Agile-and-Adaptive-Robotics/Platform/Linsey_s Documentation/screenshots/T11_L4-Center-042418.PNG

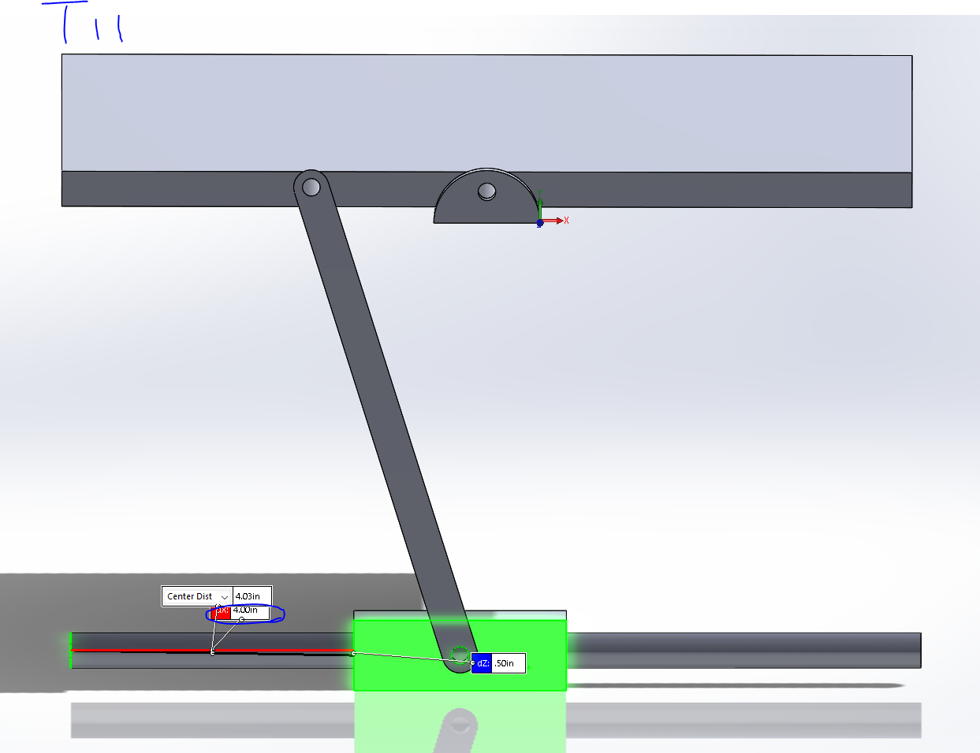
Linsey_s Documentation/screenshots/T11_L4-Center-042418.PNG
