Agile-and-Adaptive-Robotics/Platform/Linsey_s Documentation/screenshots/T2_angle-042218.PNG

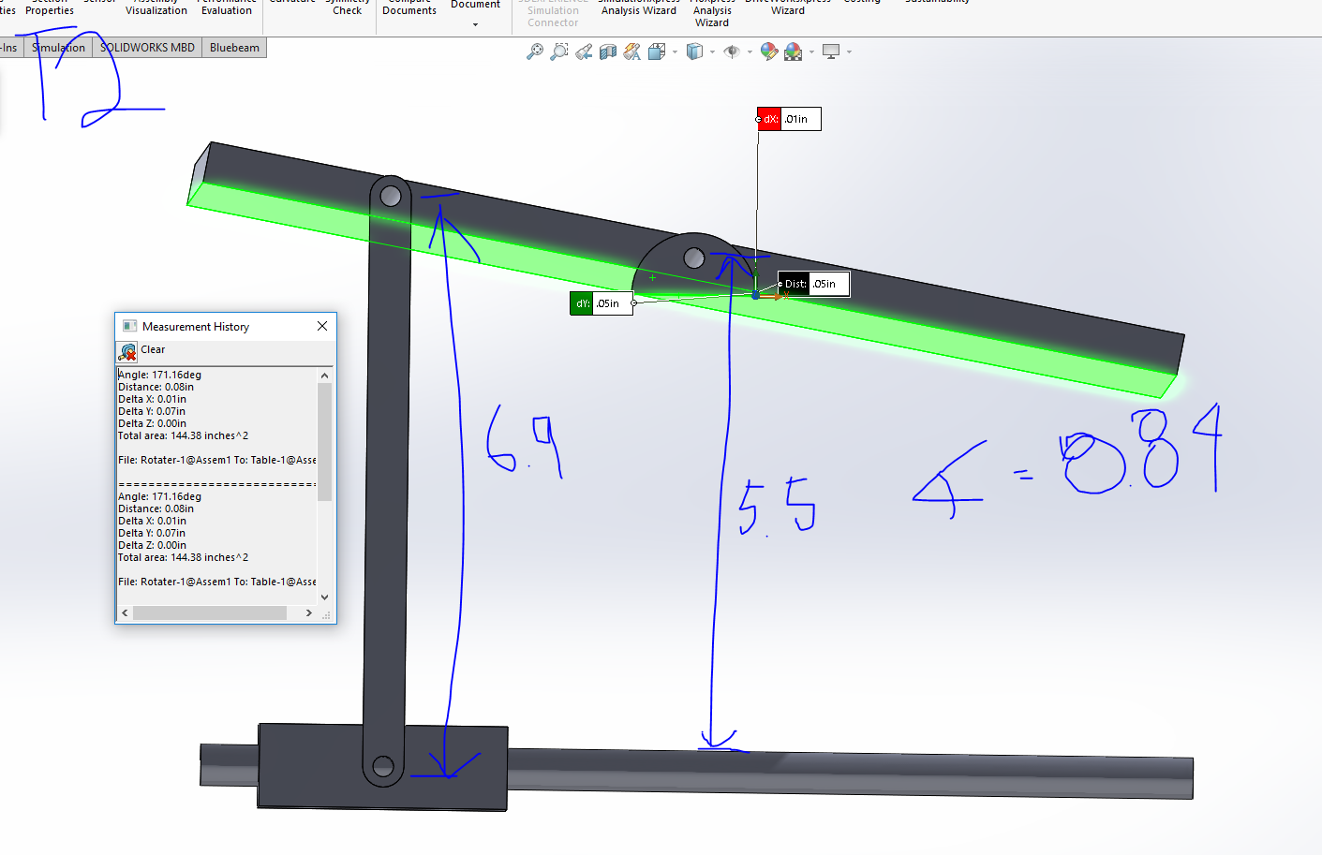
Linsey_s Documentation/screenshots/T2_angle-042218.PNG
