Agile-and-Adaptive-Robotics/Platform/Linsey_s Documentation/screenshots/T4_angle-042218.PNG

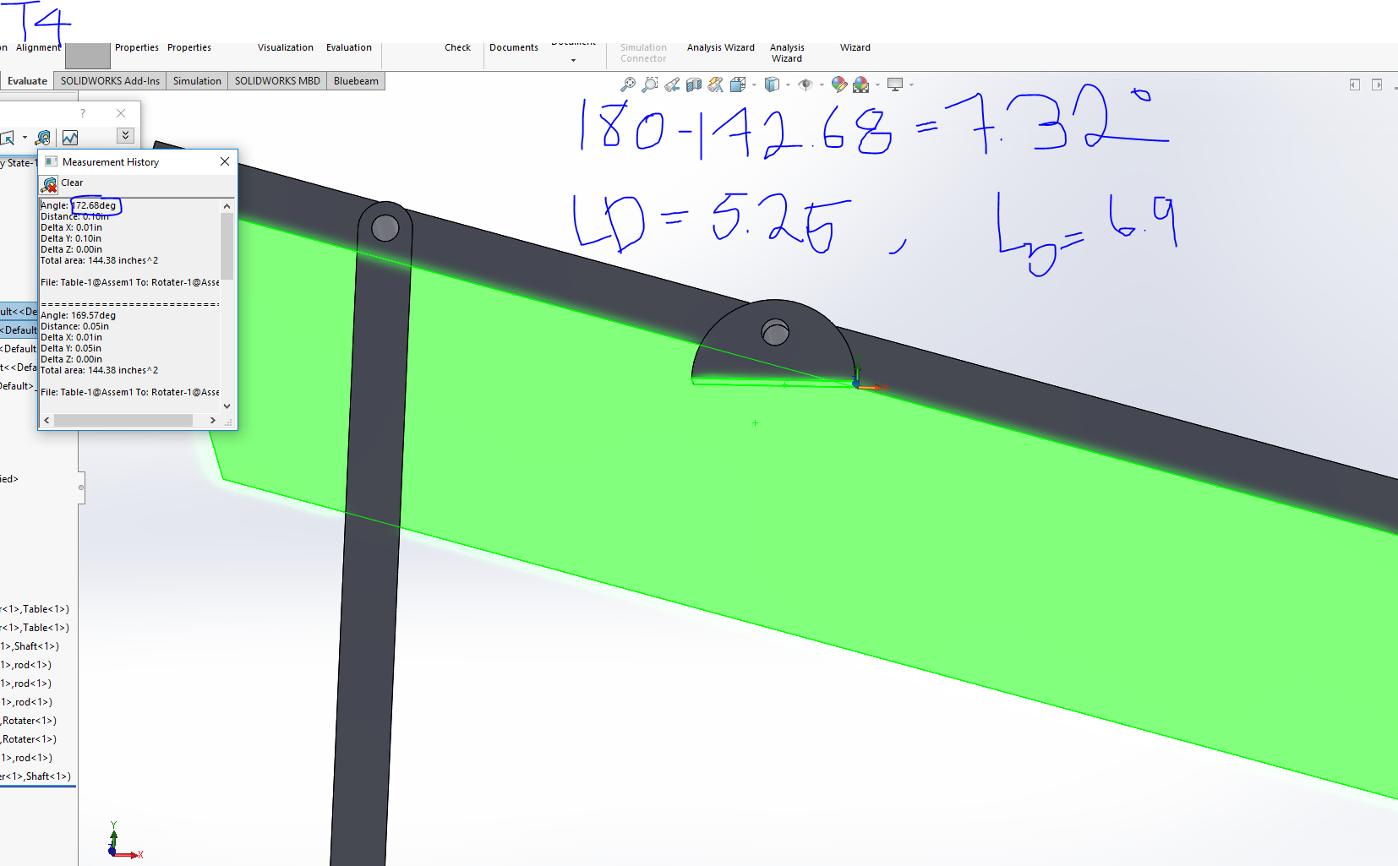
Linsey_s Documentation/screenshots/T4_angle-042218.PNG
