Agile-and-Adaptive-Robotics/Platform/Linsey_s Documentation/screenshots/T5_angle-042318.PNG

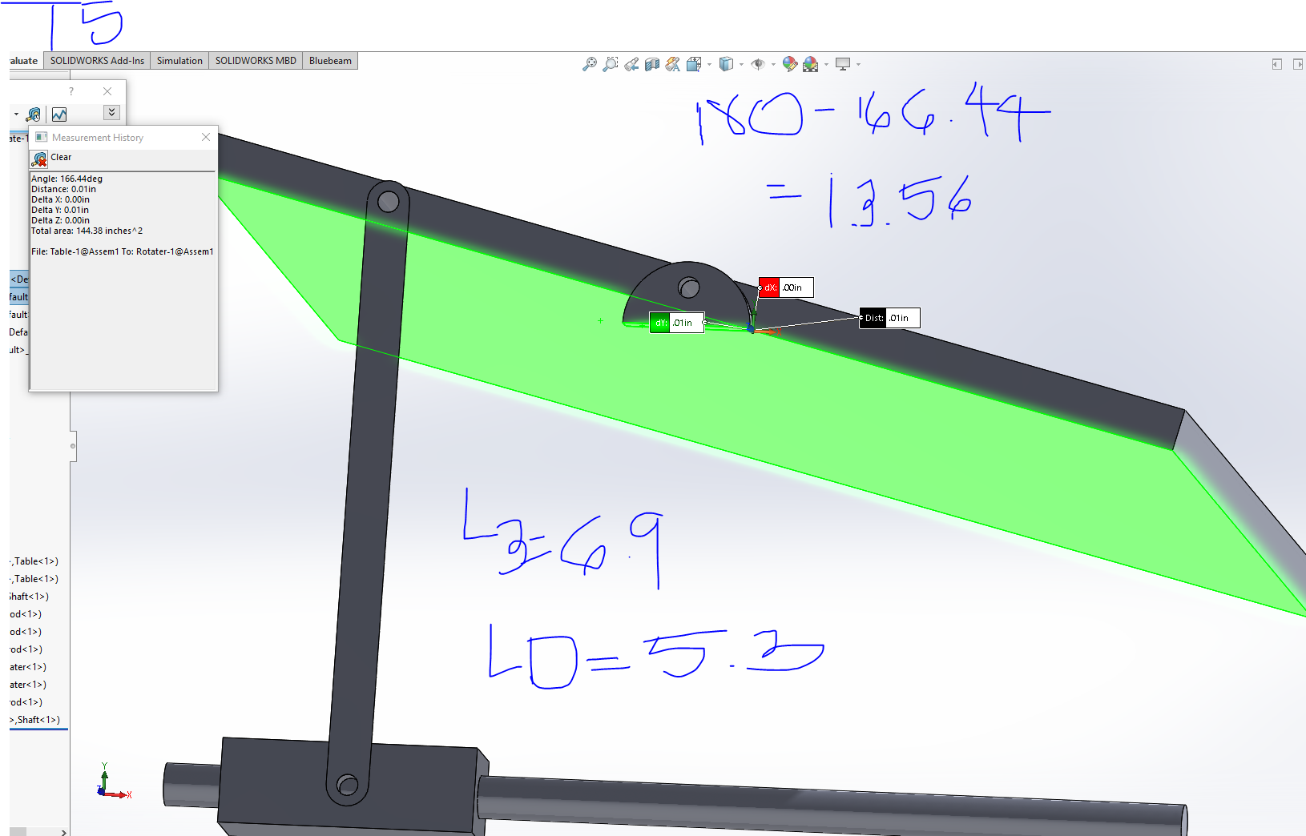
Linsey_s Documentation/screenshots/T5_angle-042318.PNG
