Agile-and-Adaptive-Robotics/Platform/Linsey_s Documentation/screenshots/T7_angle-042318.PNG

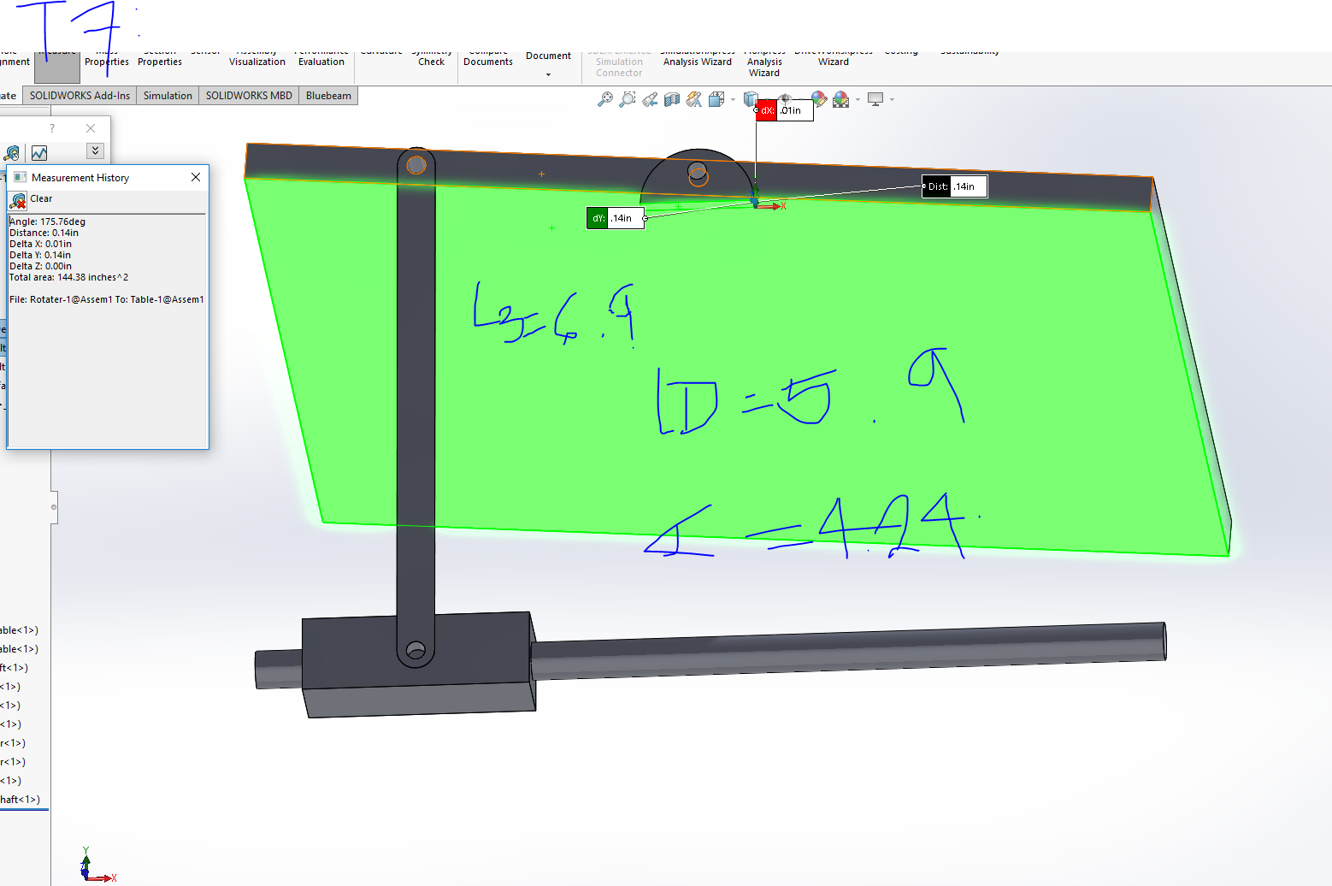
Linsey_s Documentation/screenshots/T7_angle-042318.PNG
