Agile-and-Adaptive-Robotics/Platform/Linsey_s Documentation/screenshots/T8_angle-042418-L2.PNG

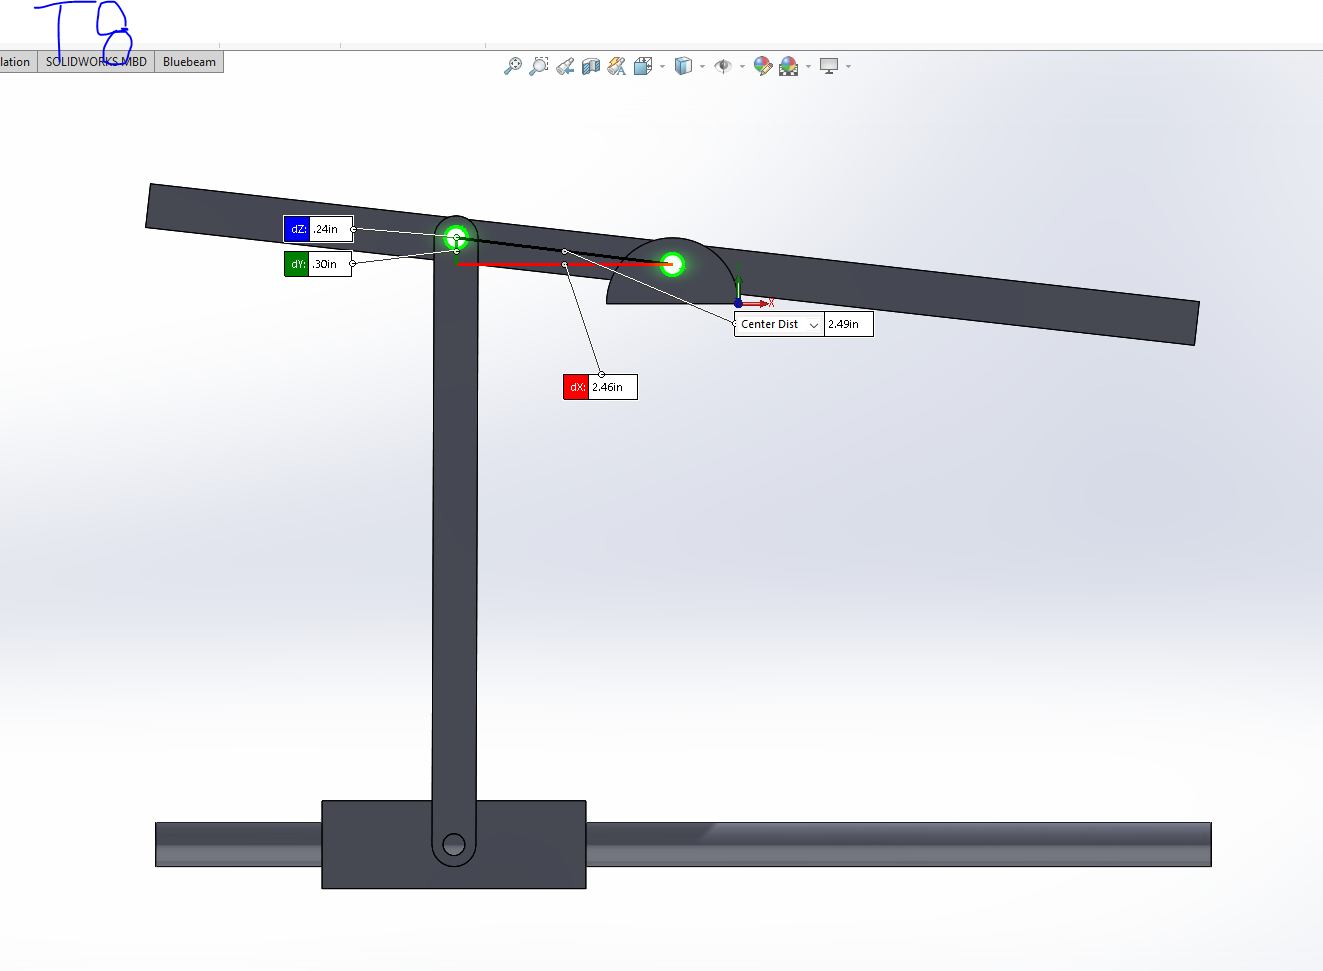
Linsey_s Documentation/screenshots/T8_angle-042418-L2.PNG
