Agile-and-Adaptive-Robotics/Platform/Linsey_s Documentation/screenshots/T9_angle-042418.PNG

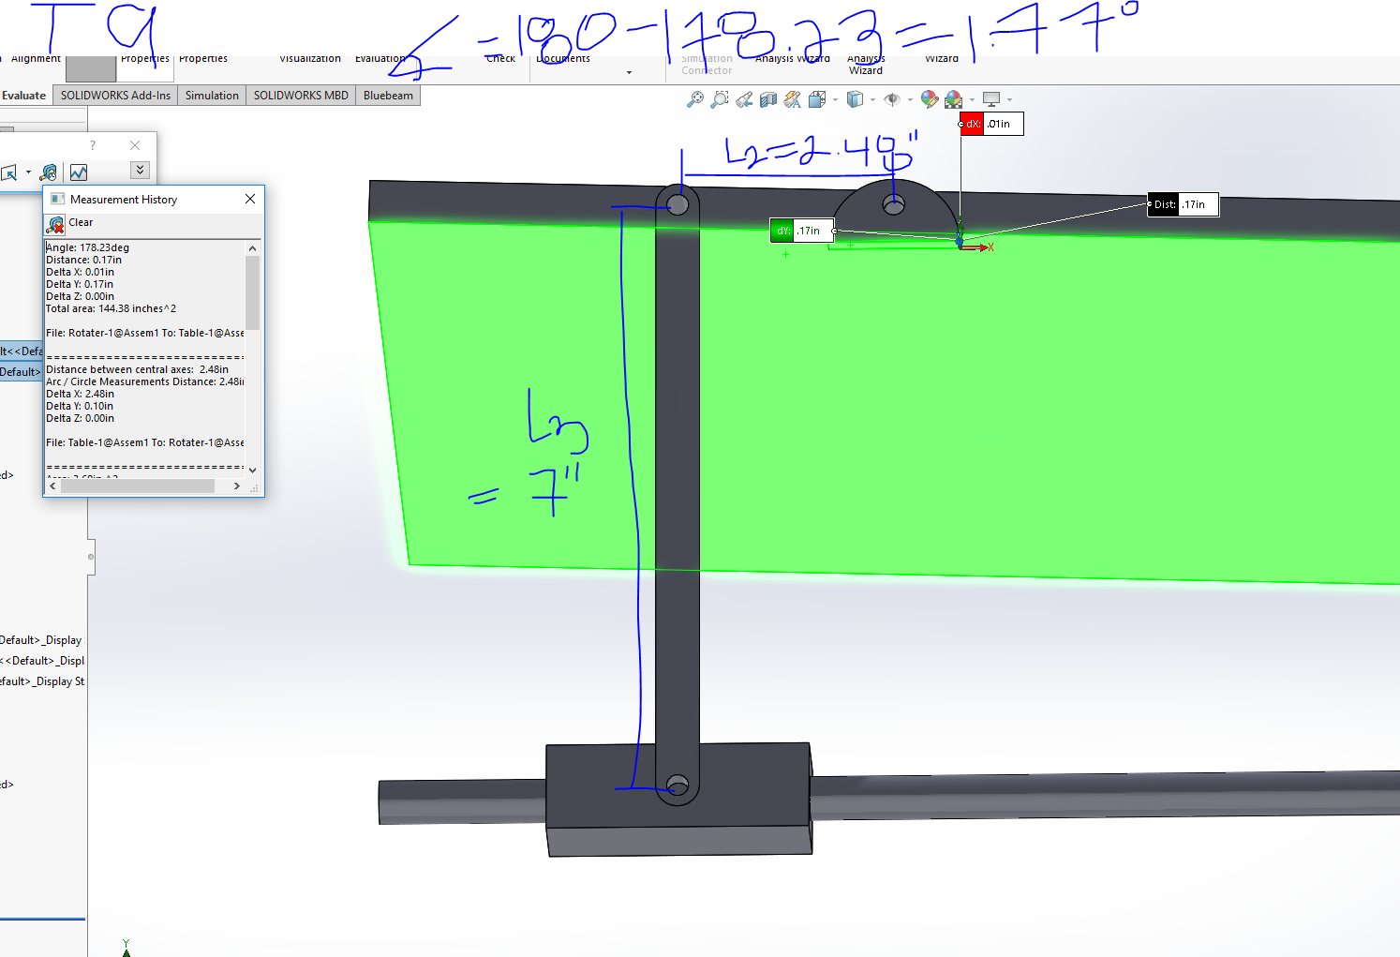
Linsey_s Documentation/screenshots/T9_angle-042418.PNG
