Agile-and-Adaptive-Robotics/Platform/Linsey_s Documentation/screenshots/T10_angle-042418.PNG

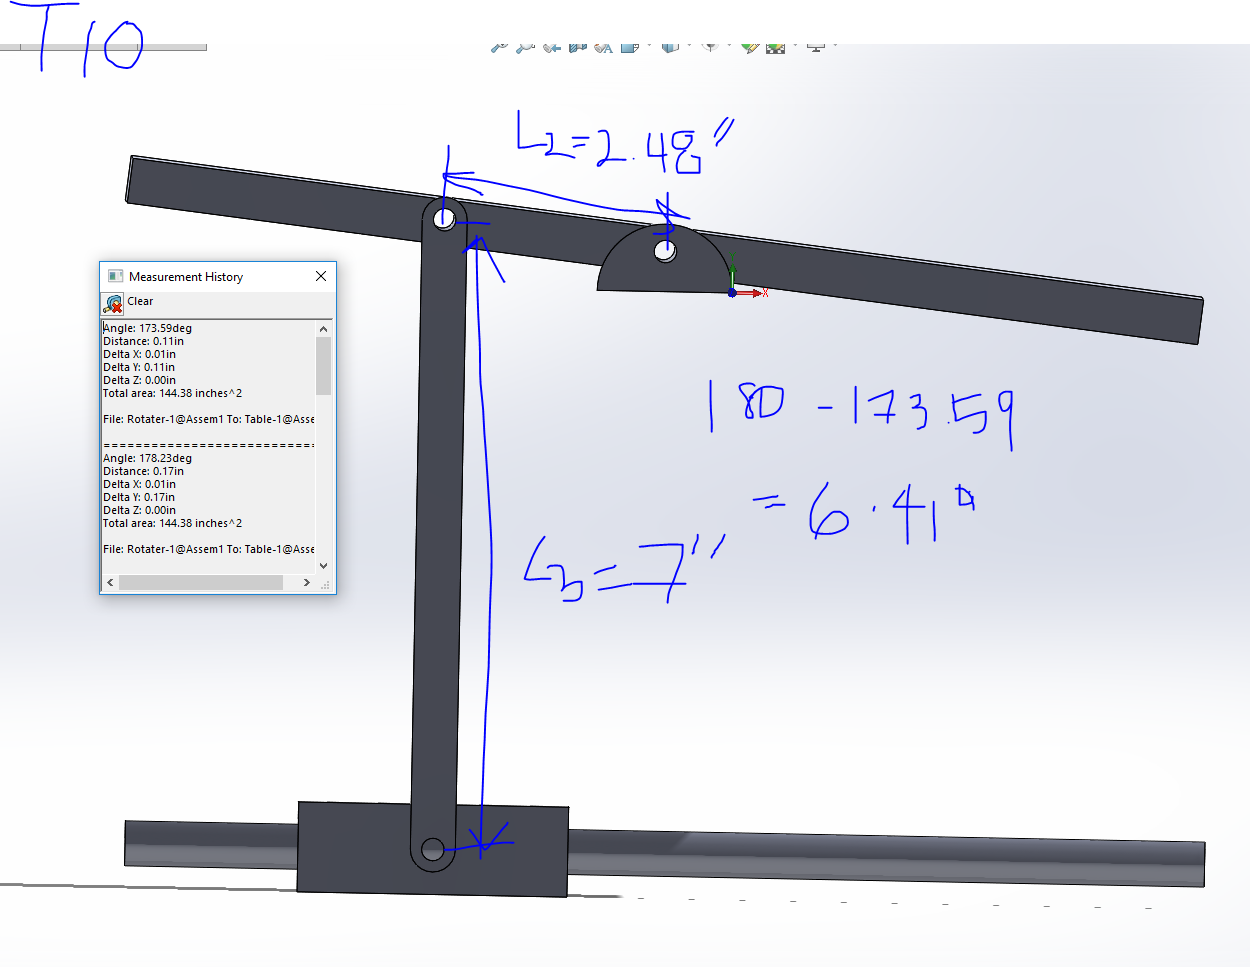
Linsey_s Documentation/screenshots/T10_angle-042418.PNG
