Agile-and-Adaptive-Robotics/Platform/Linsey_s Documentation/screenshots/T11_L4-left.PNG

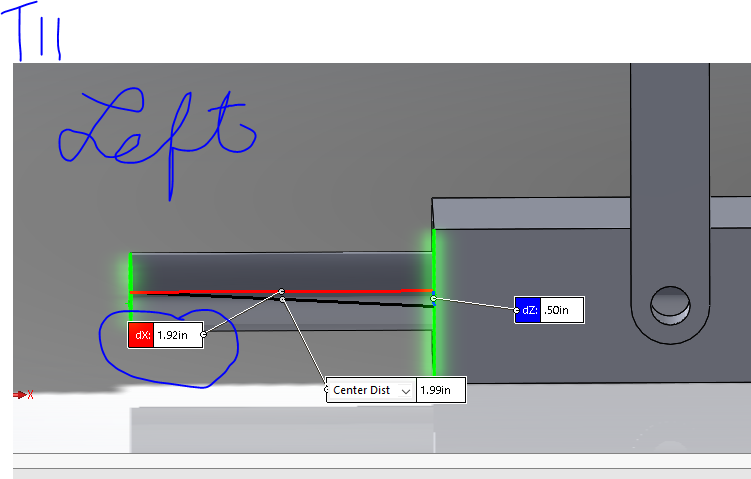
Linsey_s Documentation/screenshots/T11_L4-left.PNG
