Agile-and-Adaptive-Robotics/Platform/Linsey_s Documentation/screenshots/T11_triangles-1.PNG

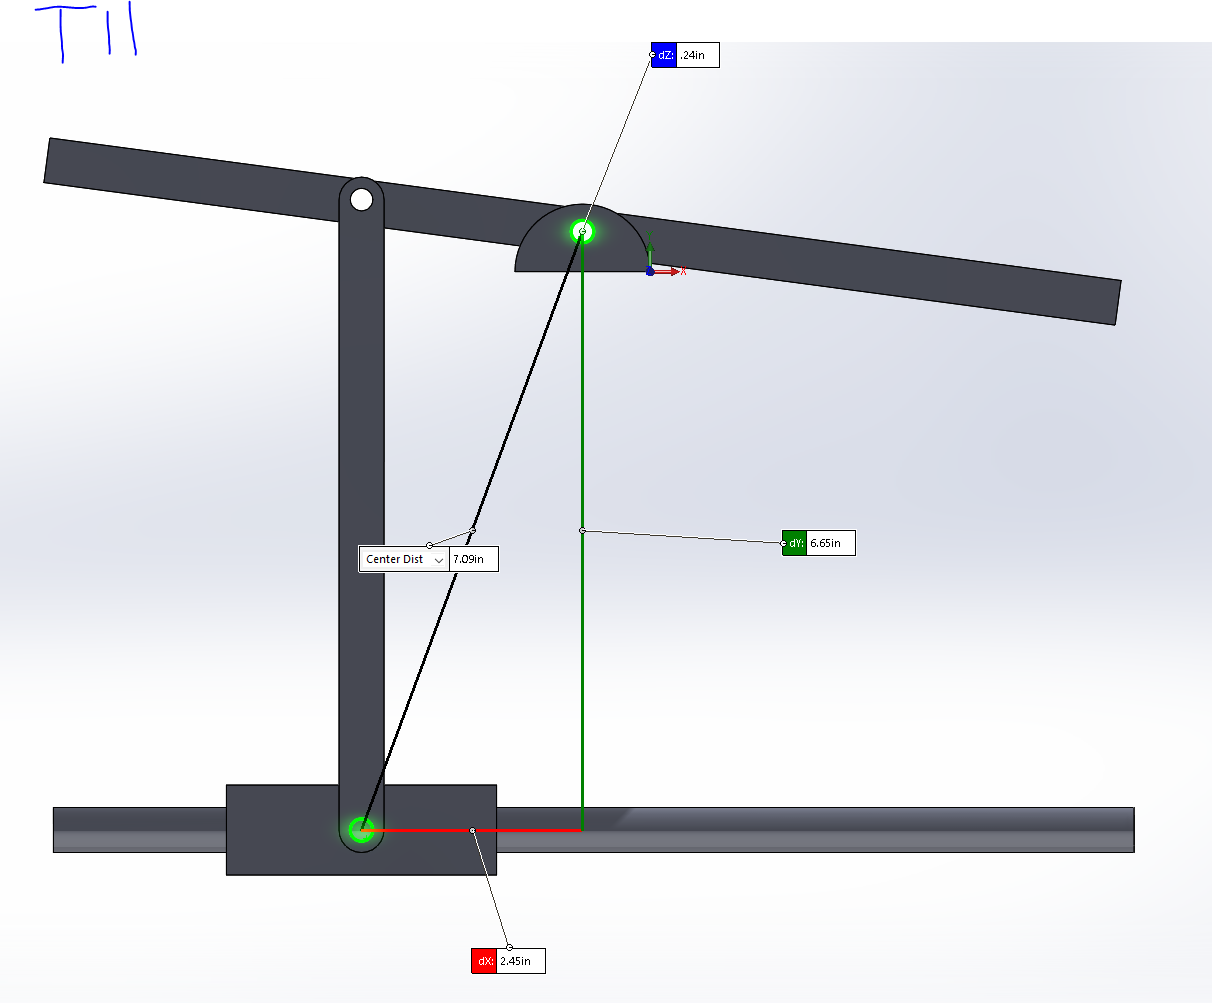
Linsey_s Documentation/screenshots/T11_triangles-1.PNG
