Agile-and-Adaptive-Robotics/Platform/Linsey_s Documentation/screenshots/Works_1-FindL4pt1.PNG

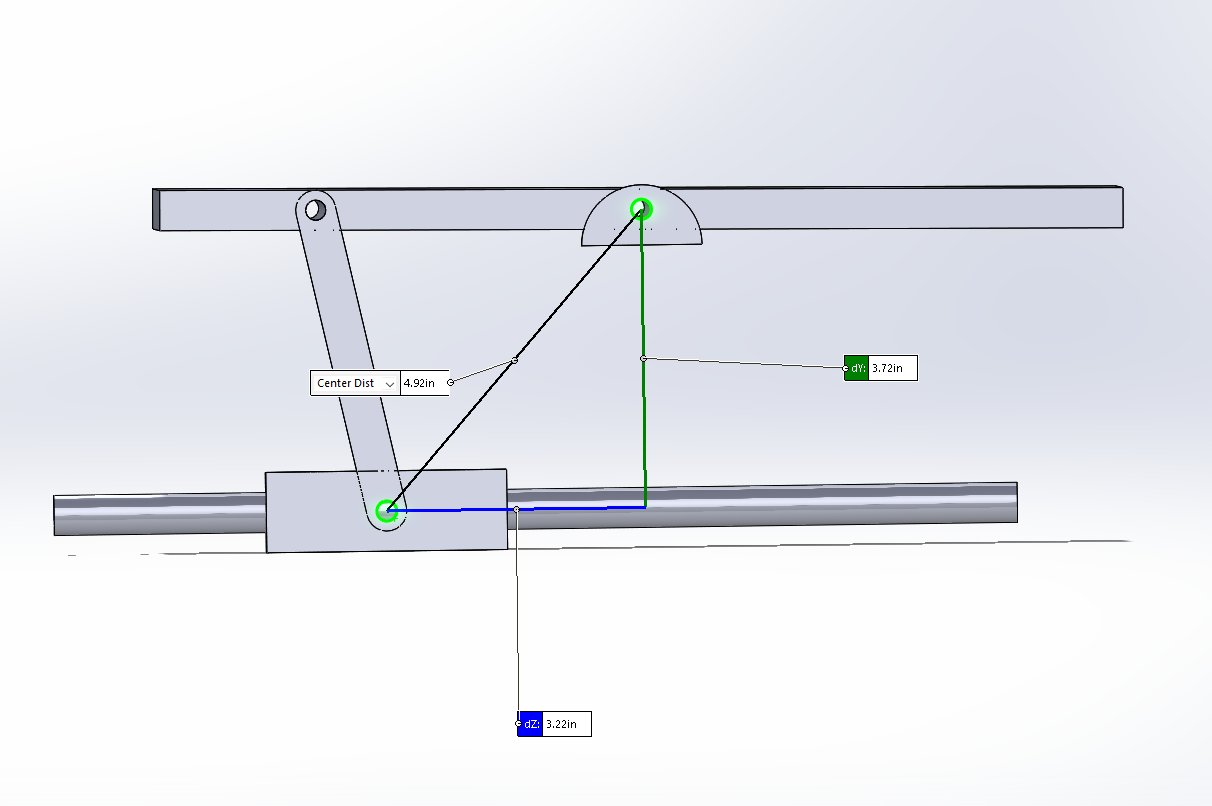
Linsey_s Documentation/screenshots/Works_1-FindL4pt1.PNG
