Agile-and-Adaptive-Robotics/Platform/Linsey_s Documentation/screenshots/Works_1-FindL4pt2.PNG

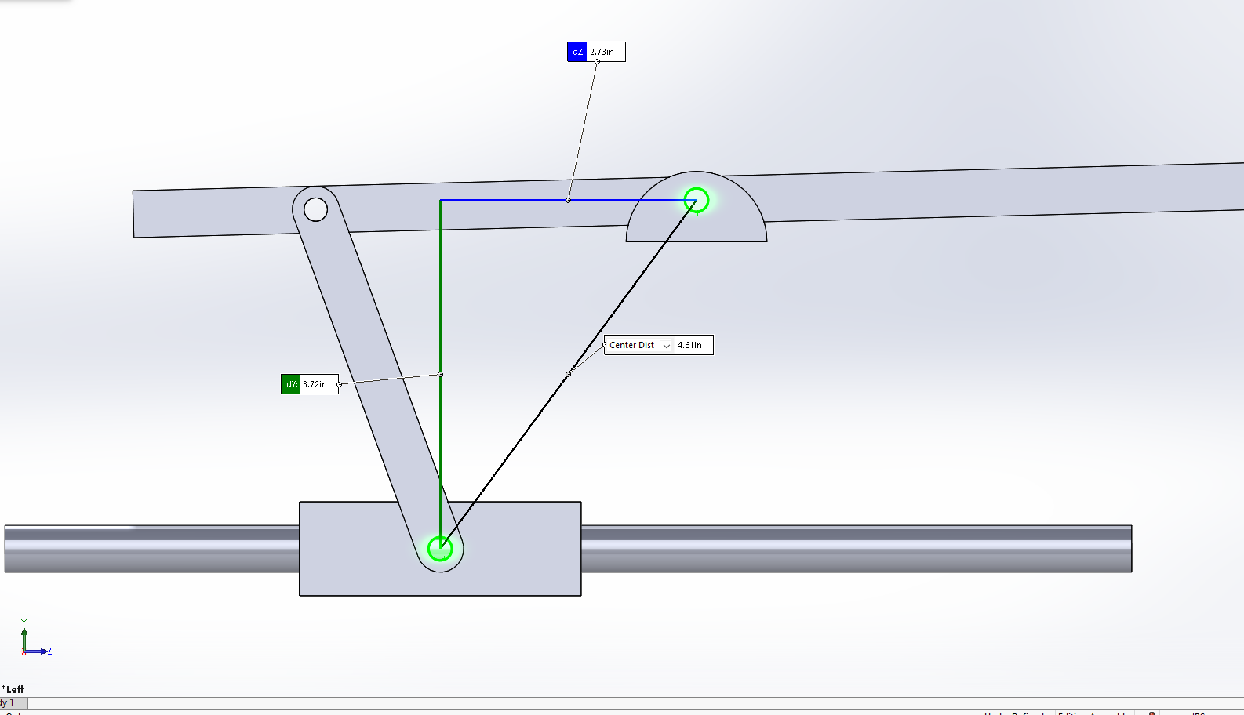
Linsey_s Documentation/screenshots/Works_1-FindL4pt2.PNG
