Agile-and-Adaptive-Robotics/Platform/Linsey_s Documentation/screenshots/Works_1.PNG

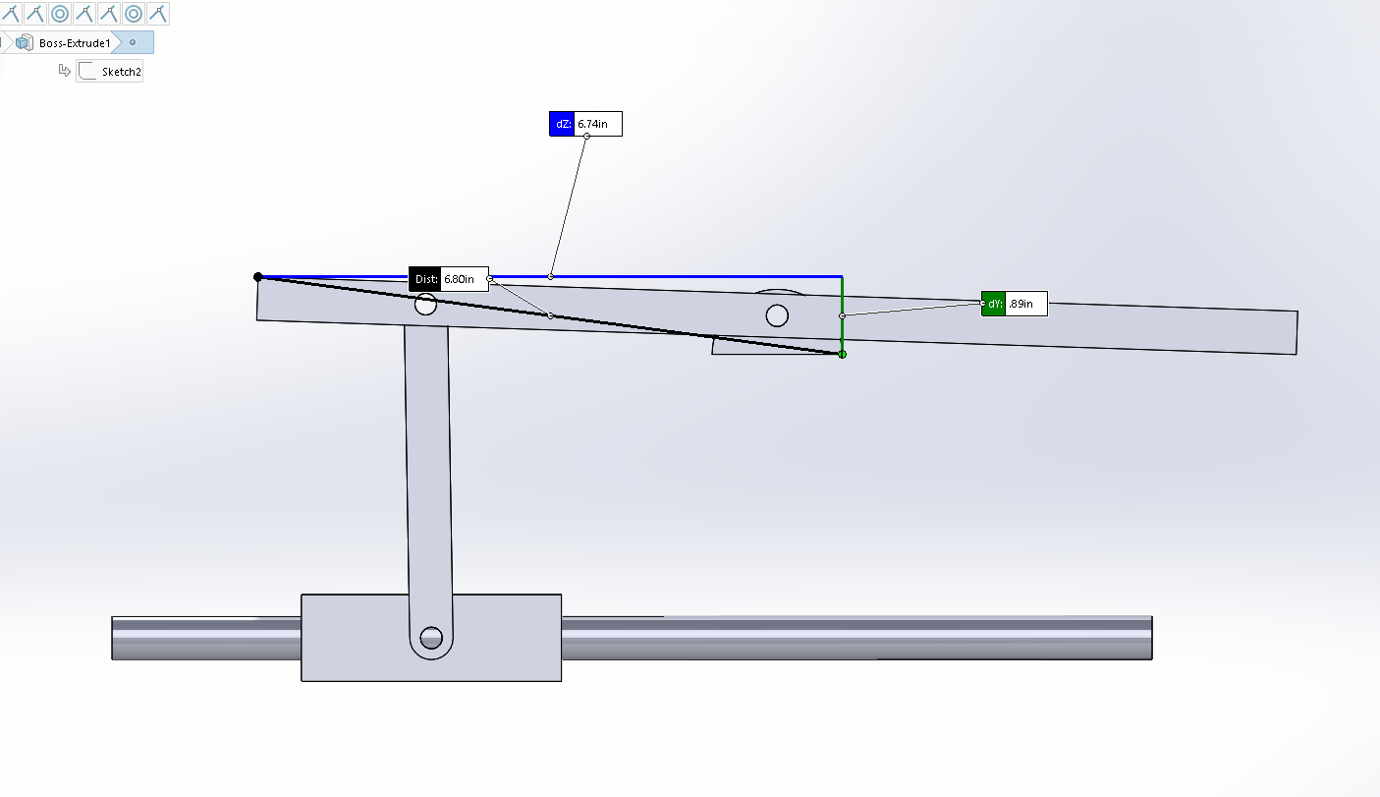
Linsey_s Documentation/screenshots/Works_1.PNG
