Agile-and-Adaptive-Robotics/Platform/Linsey_s Documentation/screenshots/works_1redo1.PNG

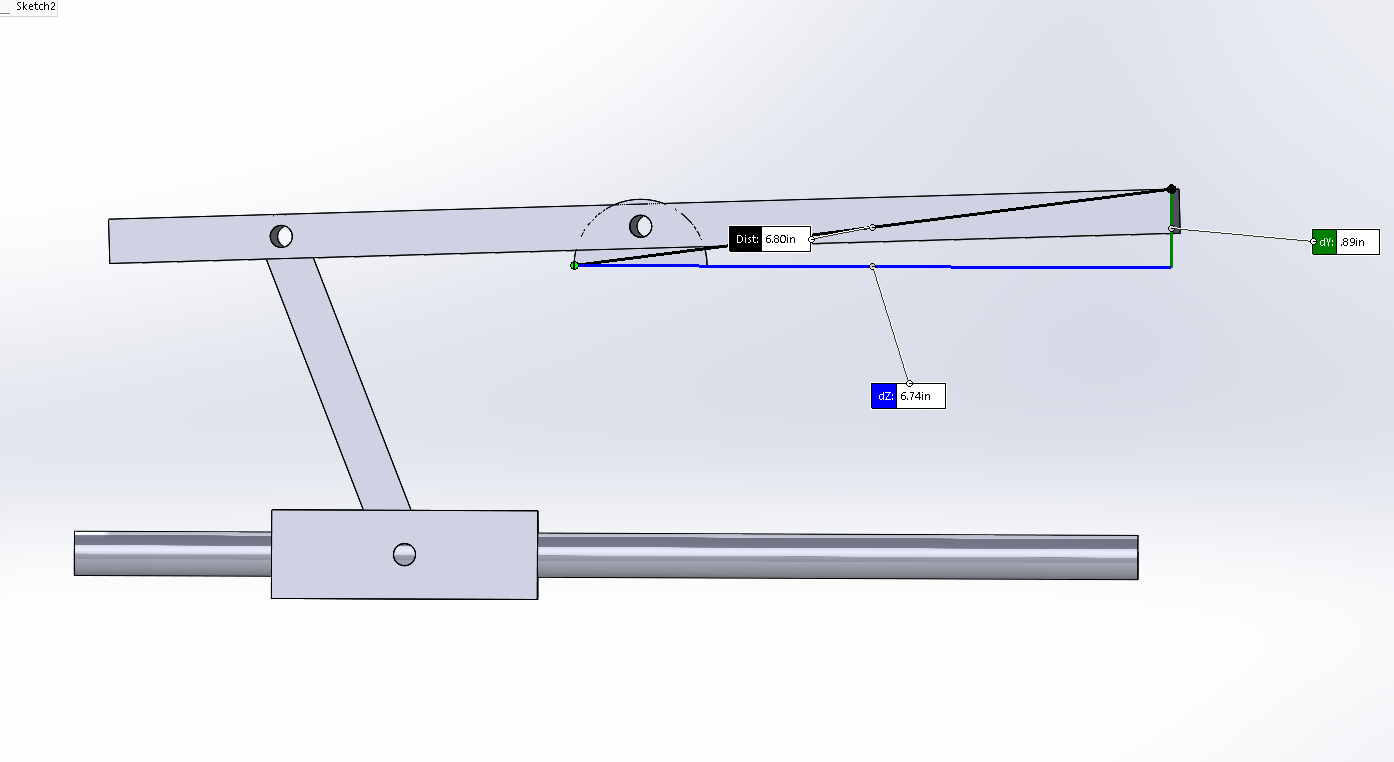
Linsey_s Documentation/screenshots/works_1redo1.PNG
