Agile-and-Adaptive-Robotics/Platform/Solidworks Files/jakesDesign/userInterfaceMounting.SLDPRT

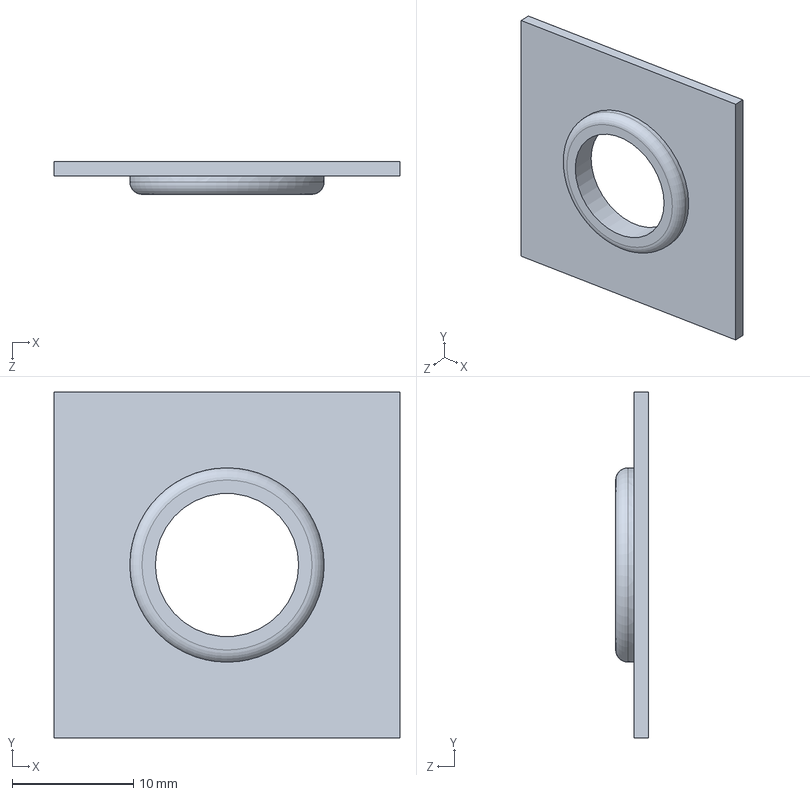
[picture p41: CAD file, 2020-02-07]
Solidworks Files/jakesDesign/userInterfaceMounting.SLDPRT
28.5 x 28.5 x 2.70 mm
