Agile-and-Adaptive-Robotics/Platform/Linsey_s Documentation/Solidworks in use/not 3dprinted stuff/1515_9.SLDPRT

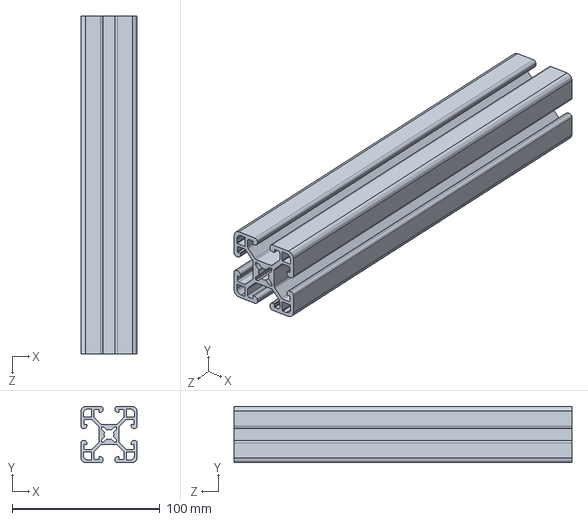
[picture p42: CAD file, 2019-10-21]
Linsey_s Documentation/Solidworks in use/not 3dprinted stuff/1515_9.SLDPRT
38.1 x 38.1 x 228.6 mm
