Agile-and-Adaptive-Robotics/Platform/Linsey_s Documentation/Solidworks in use/not 3dprinted stuff/1515_15.SLDPRT

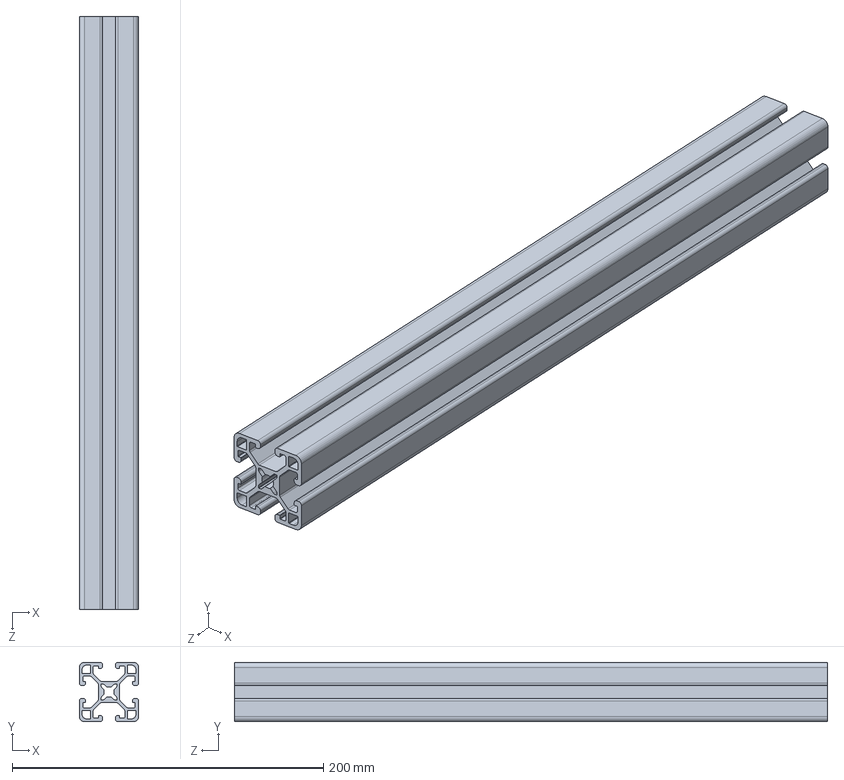
[picture p43: CAD file, 2019-10-21]
Linsey_s Documentation/Solidworks in use/not 3dprinted stuff/1515_15.SLDPRT
38.1 x 38.1 x 381.0 mm
