Agile-and-Adaptive-Robotics/Platform/Solidworks Files/BP_Arduino_Controls_Housing_1.SLDPRT

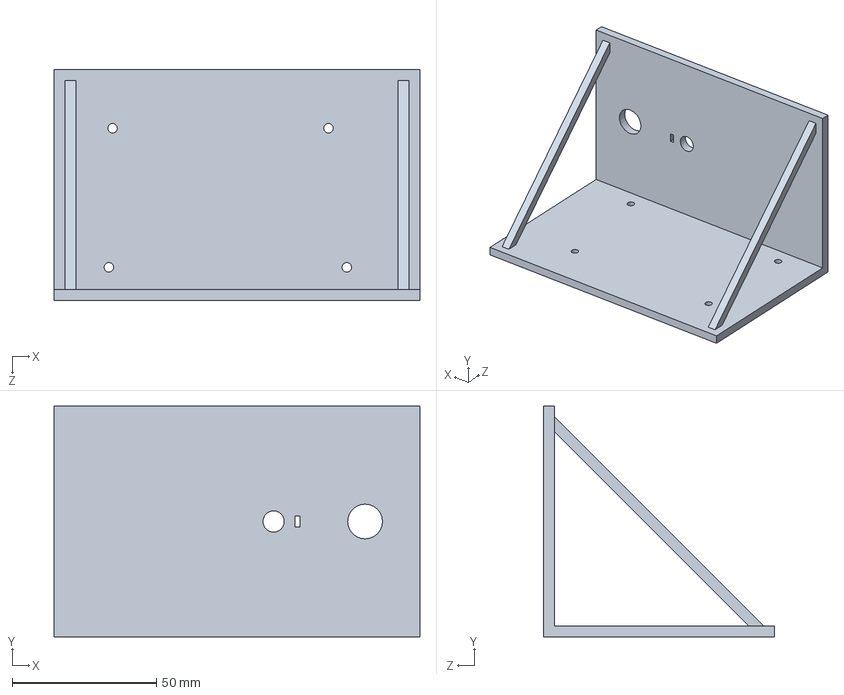
[picture p44: CAD file, 2019-10-21]
Solidworks Files/BP_Arduino_Controls_Housing_1.SLDPRT
127.0 x 80.0 x 80.0 mm
