Agile-and-Adaptive-Robotics/Platform/Linsey_s Documentation/Solidworks in use/insert.SLDPRT

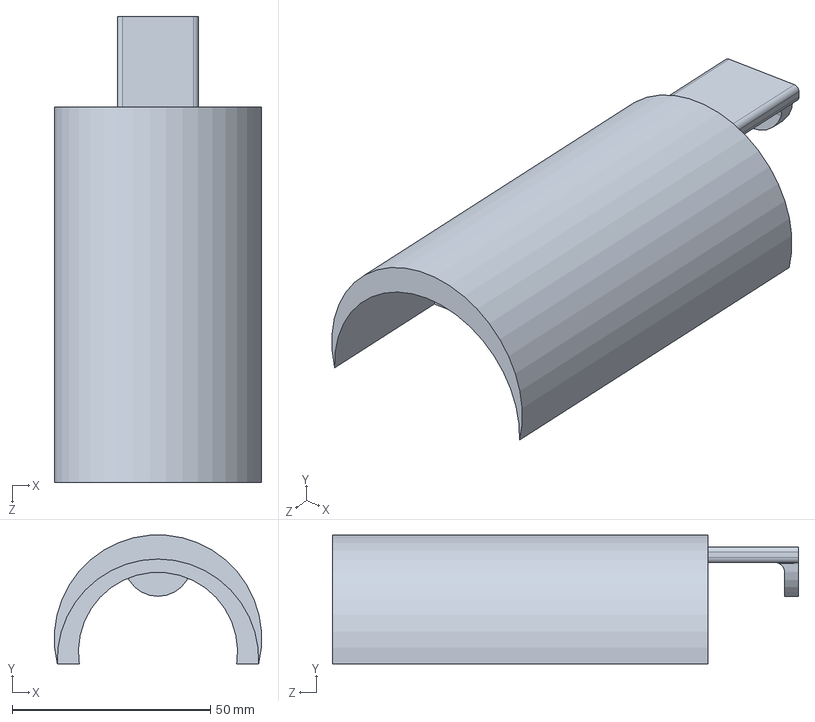
[picture p45: CAD file, 2019-10-21]
Linsey_s Documentation/Solidworks in use/insert.SLDPRT
52.2 x 32.4 x 117.6 mm
