Agile-and-Adaptive-Robotics/Platform/Linsey_s Documentation/Solidworks in use/not 3dprinted stuff/rotty.SLDPRT

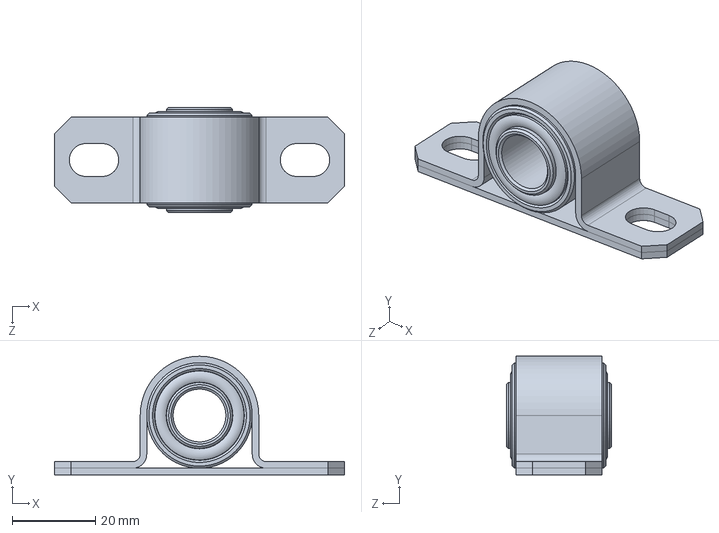
[picture p46: CAD file, 2019-10-21]
Linsey_s Documentation/Solidworks in use/not 3dprinted stuff/rotty.SLDPRT
69.8 x 28.6 x 25.4 mm
