Agile-and-Adaptive-Robotics/Platform/Linsey_s Documentation/Solidworks in use/not 3dprinted stuff/bigrot.SLDPRT

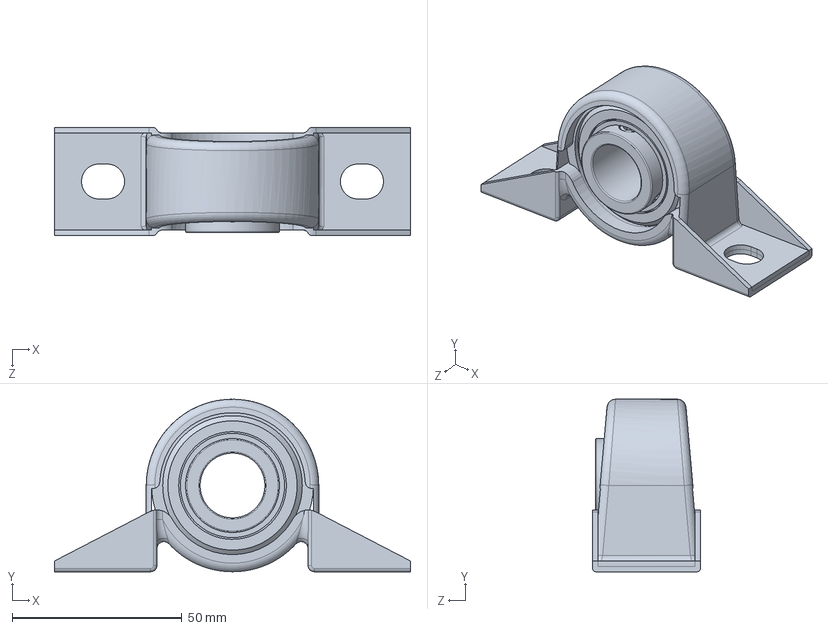
[picture p47: CAD file, 2019-10-21]
Linsey_s Documentation/Solidworks in use/not 3dprinted stuff/bigrot.SLDPRT
104.8 x 50.8 x 31.8 mm
