Agile-and-Adaptive-Robotics/Platform/Linsey_s Documentation/Solidworks in use/simp_coup.SLDPRT

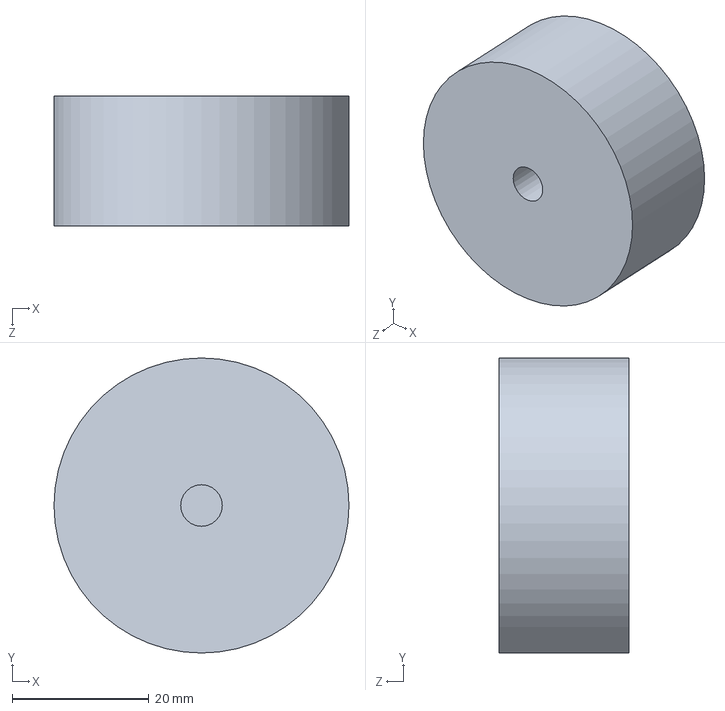
[picture p48: CAD file, 2019-10-21]
Linsey_s Documentation/Solidworks in use/simp_coup.SLDPRT
43.2 x 43.2 x 19.1 mm
