Agile-and-Adaptive-Robotics/Platform/Linsey_s Documentation/Solidworks in use/jacks_coupler.SLDPRT

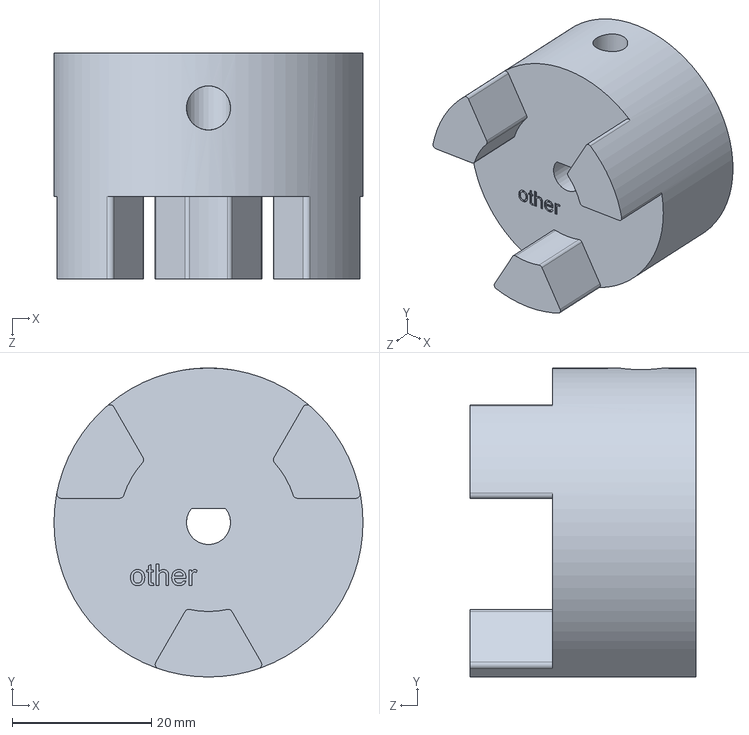
[picture p49: CAD file, 2019-10-21]
Linsey_s Documentation/Solidworks in use/jacks_coupler.SLDPRT
44.5 x 44.5 x 32.4 mm
