Agile-and-Adaptive-Robotics/Platform/Linsey_s Documentation/Solidworks in use/not 3dprinted stuff/tiny_bear.SLDPRT

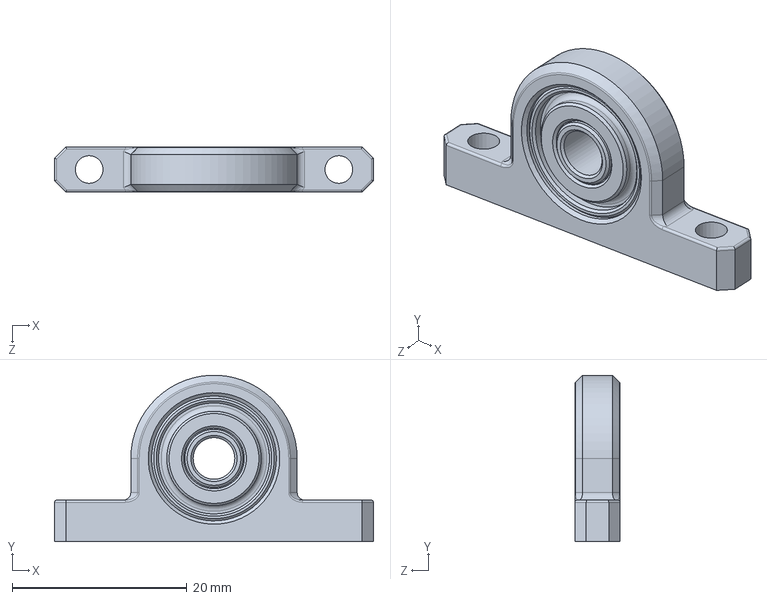
[picture p50: CAD file, 2019-10-21]
Linsey_s Documentation/Solidworks in use/not 3dprinted stuff/tiny_bear.SLDPRT
36.5 x 19.0 x 5.16 mm
