Agile-and-Adaptive-Robotics/Platform/Solidworks Files/BP_Pot_Holder_1.SLDPRT

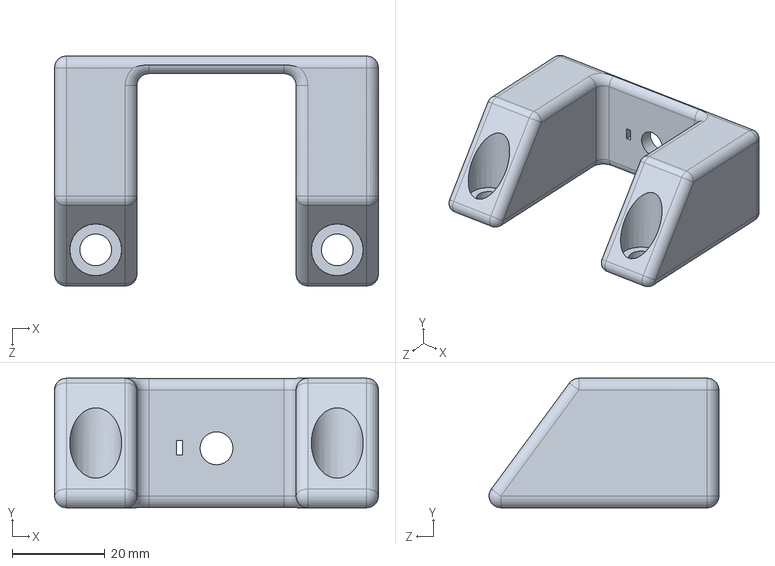
[picture p51: CAD file, 2019-10-21]
Solidworks Files/BP_Pot_Holder_1.SLDPRT
69.8 x 27.9 x 49.6 mm
