Agile-and-Adaptive-Robotics/Platform/Linsey_s Documentation/Solidworks in use/Spider - fixed by cody.SLDPRT

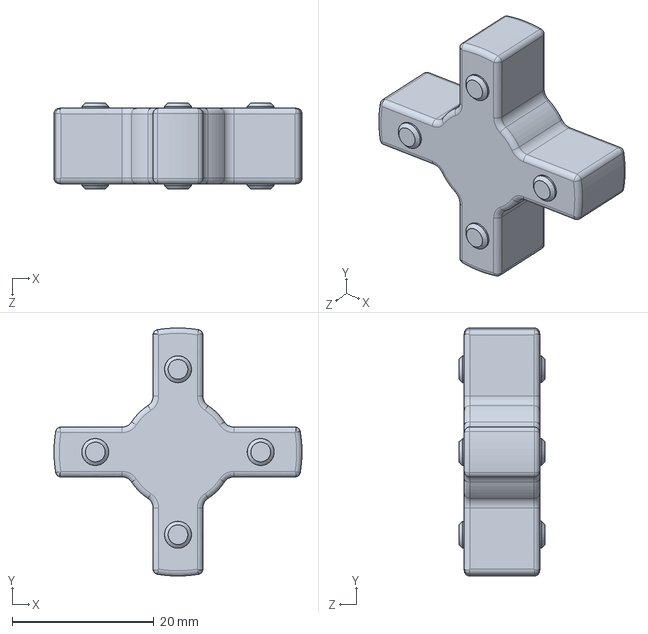
[picture p52: CAD file, 2019-10-21]
Linsey_s Documentation/Solidworks in use/Spider - fixed by cody.SLDPRT
35.0 x 35.0 x 12.2 mm
