Agile-and-Adaptive-Robotics/Platform/Solidworks Files/BP_Pot_Shaft_Interface_1.SLDPRT

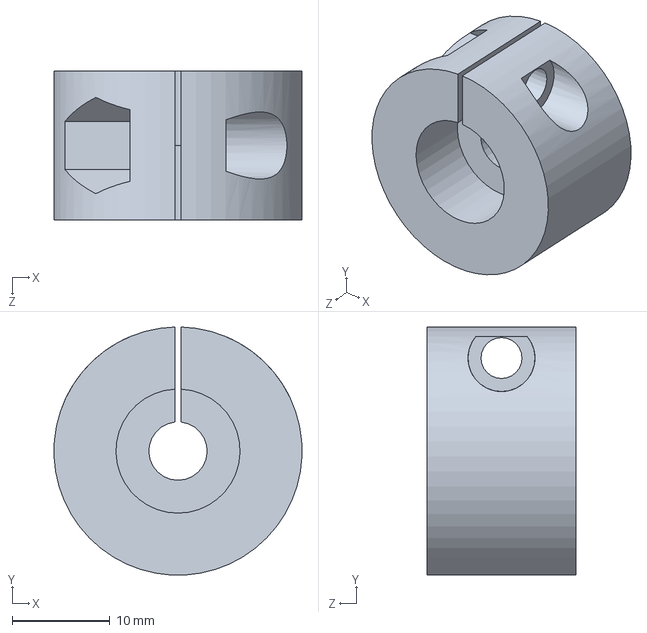
[picture p53: CAD file, 2019-10-21]
Solidworks Files/BP_Pot_Shaft_Interface_1.SLDPRT
25.4 x 25.4 x 15.2 mm
